liveboxandy/Gotek-Compatible-AT32F435-26Pin-SMD/STP/1188E-1K2-V-T_R.stp

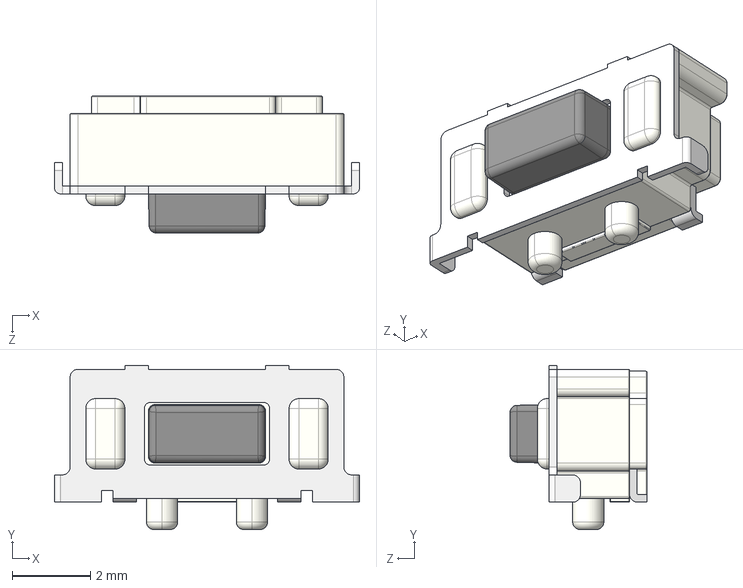
[picture p17: CAD file, 2025-10-23]
STP/1188E-1K2-V-T_R.stp
7.80 x 4.20 x 3.50 mm
