liveboxandy/Gotek-Compatible-AT32F435-26Pin-SMD/STP/SKRTLAE010.stp

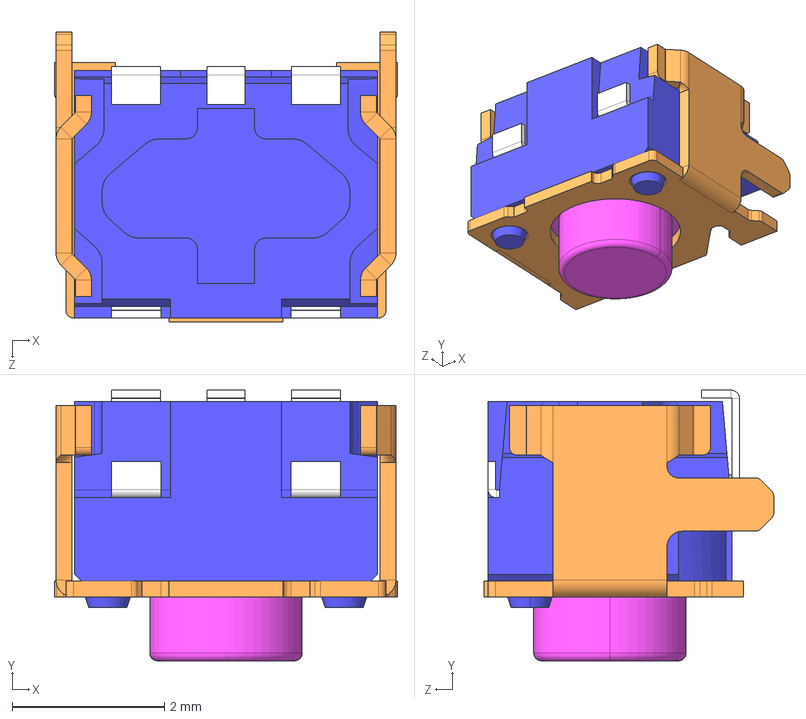
[picture p18: CAD file, 2025-10-23]
STP/SKRTLAE010.stp
4.50 x 3.55 x 3.80 mm
