liveboxandy/Gotek-Compatible-AT32F435-26Pin-SMD/STP/1N4148WS.stp

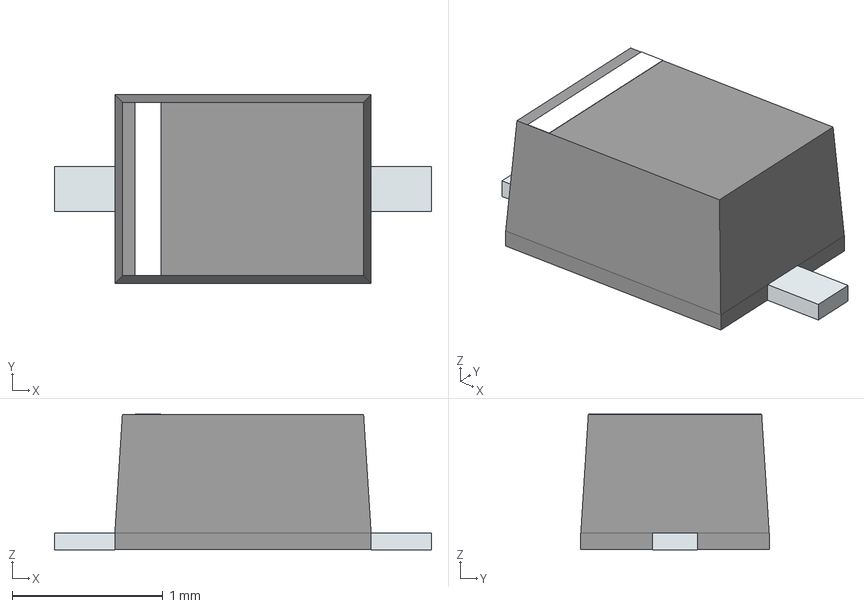
[picture p19: CAD file, 2025-10-23]
STP/1N4148WS.stp
2.50 x 1.25 x 0.9 mm
PinKIdent
PinK
PinA
