liveboxandy/Gotek-Compatible-AT32F435-26Pin-SMD/STP/Molex 2005280260.stp

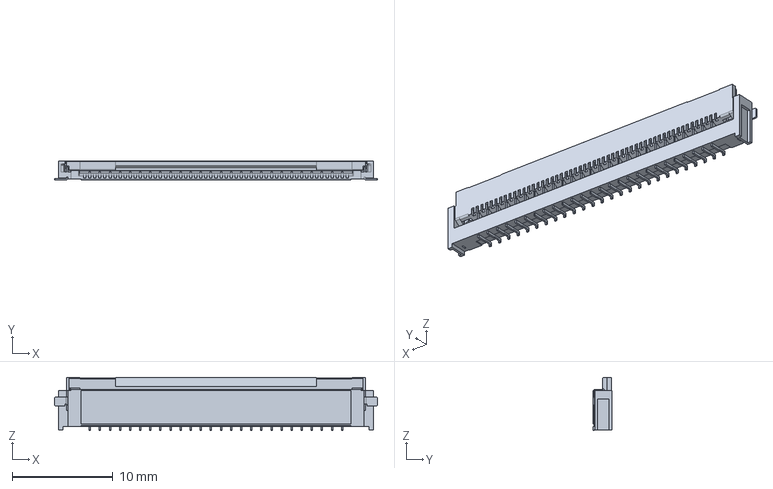
[picture p20: CAD file, 2025-10-23]
STP/Molex 2005280260.stp
32.0 x 1.90 x 5.30 mm
