liveboxandy/Gotek-Compatible-AT32F435-26Pin-SMD/STP/ABL-8.000MHZ-B2.stp

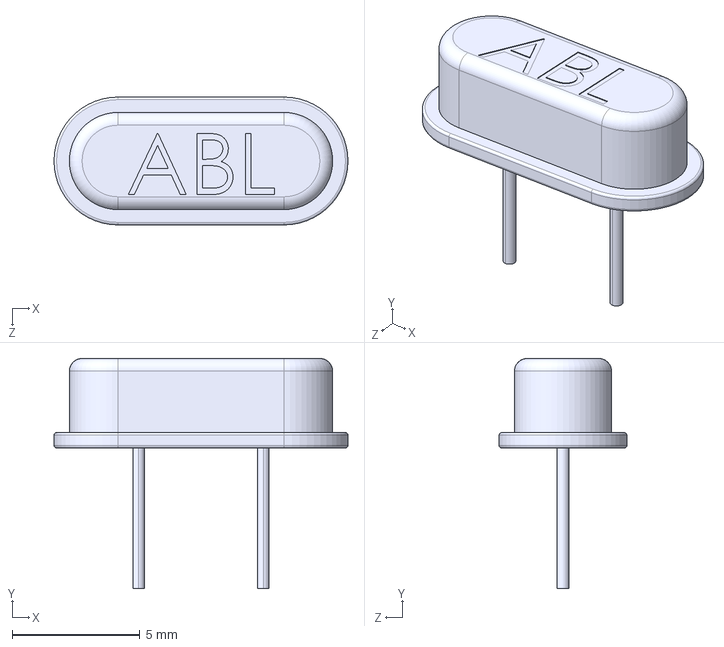
[picture p21: CAD file, 2025-10-23]
STP/ABL-8.000MHZ-B2.stp
11.5 x 9.00 x 5.00 mm
