liveboxandy/Gotek-Compatible-AT32F435-26Pin-SMD/STP/TSM-107-01-L-SH.stp

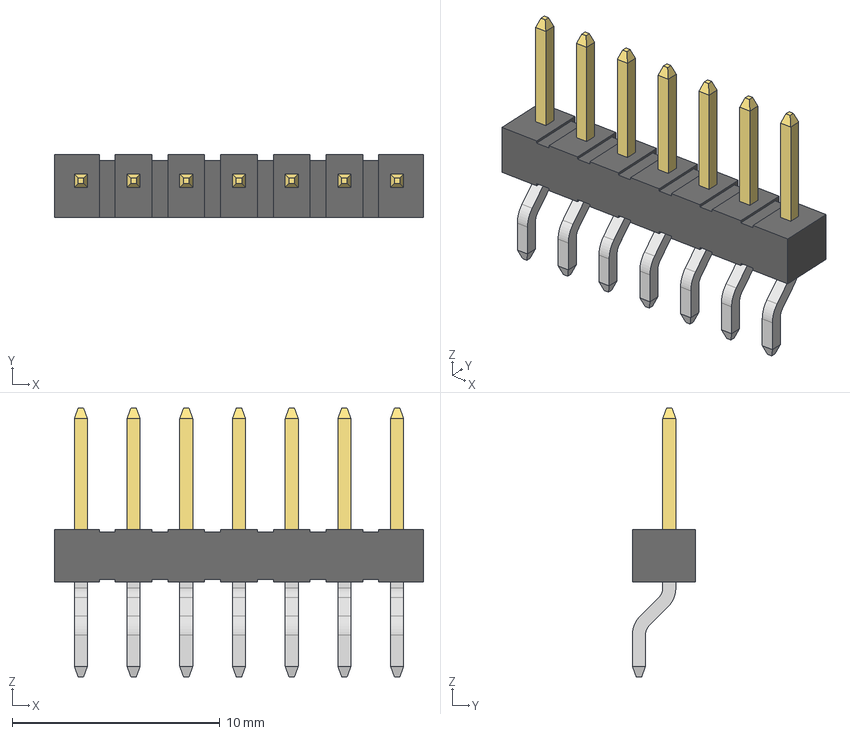
[picture p22: CAD file, 2025-10-23]
STP/TSM-107-01-L-SH.stp
17.8 x 3.05 x 13.0 mm
TSM-107-01-SH_body
T-1S6-08-L(-01-7-SH)
T-1S6-08-L(-01-7-SH)2
