liveboxandy/Gotek-Compatible-AT32F435-26Pin-SMD/STP/TSM-105-04-S-DV.stp

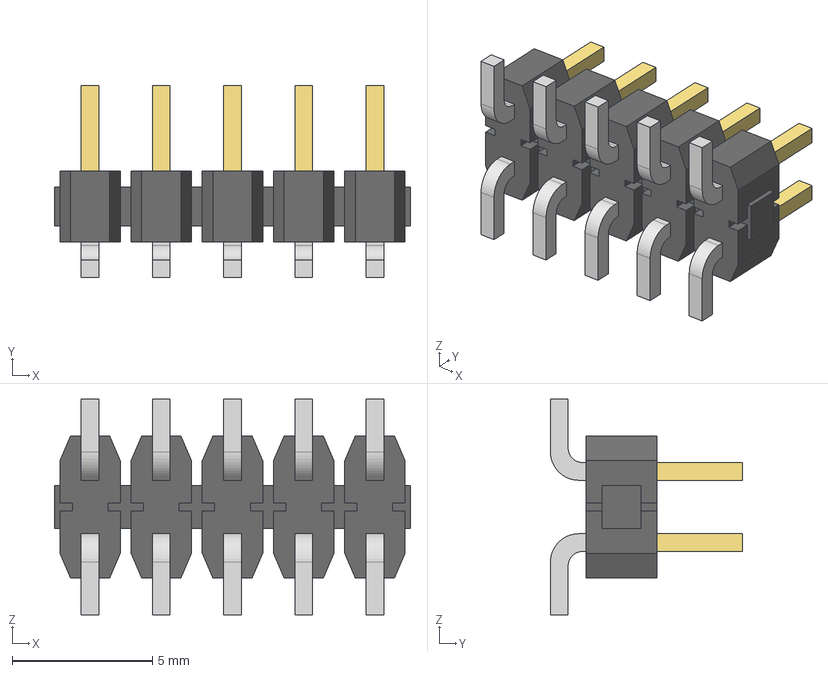
[picture p23: CAD file, 2025-10-23]
STP/TSM-105-04-S-DV.stp
12.7 x 6.86 x 7.70 mm
TSM-105-04-DV_body
T-1S6-21-S(-04-5-DV)
T-1S6-21-S(-04-5-DV)2
