liveboxandy/Gotek-Compatible-AT32F435-26Pin-SMD/STP/USB1055-GF-L-A.stp

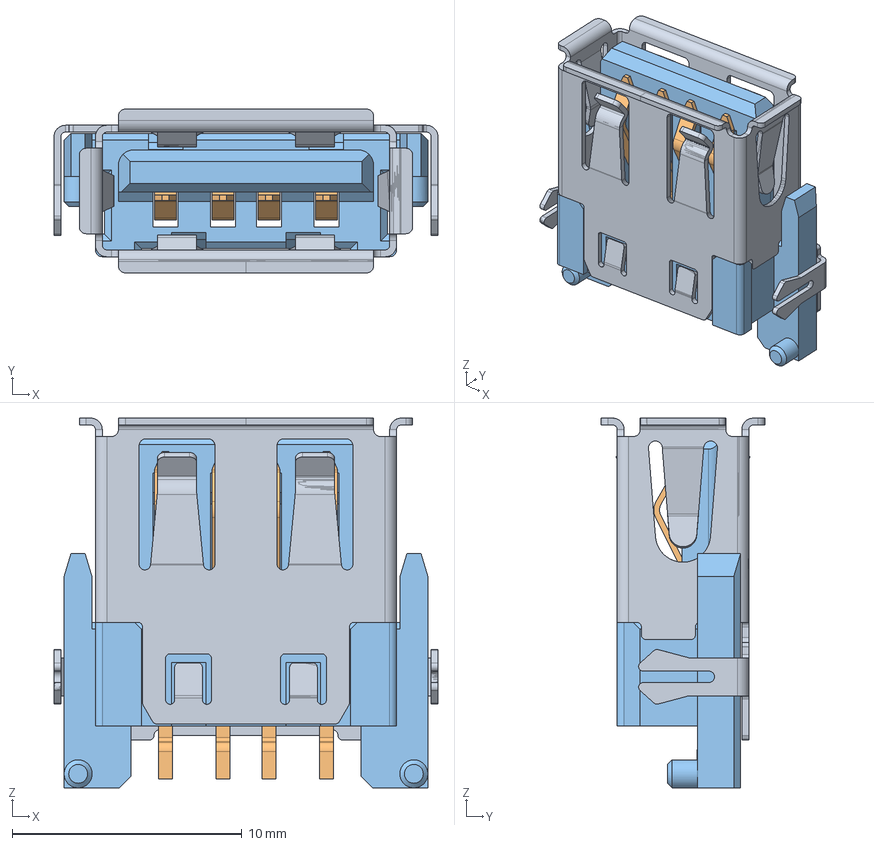
[picture p24: CAD file, 2025-10-23]
STP/USB1055-GF-L-A.stp
16.7 x 7.12 x 16.1 mm
USB1055-GF-L-A_PART8
USB1055-GF-L-A_PART7
USB1055-GF-L-A_PART6
USB1055-GF-L-A_PART5
USB1055-GF-L-A_PART4
USB1055-GF-L-A_PART3
USB1055-GF-L-A_PART2
USB1055-GF-L-A_PART1
