liveboxandy/Gotek-Compatible-AT32F435-26Pin-SMD/3V3To5VConversion.kicad_sch

## KiCad design 3V3To5VConversion.kicad_sch (2025-10-23)

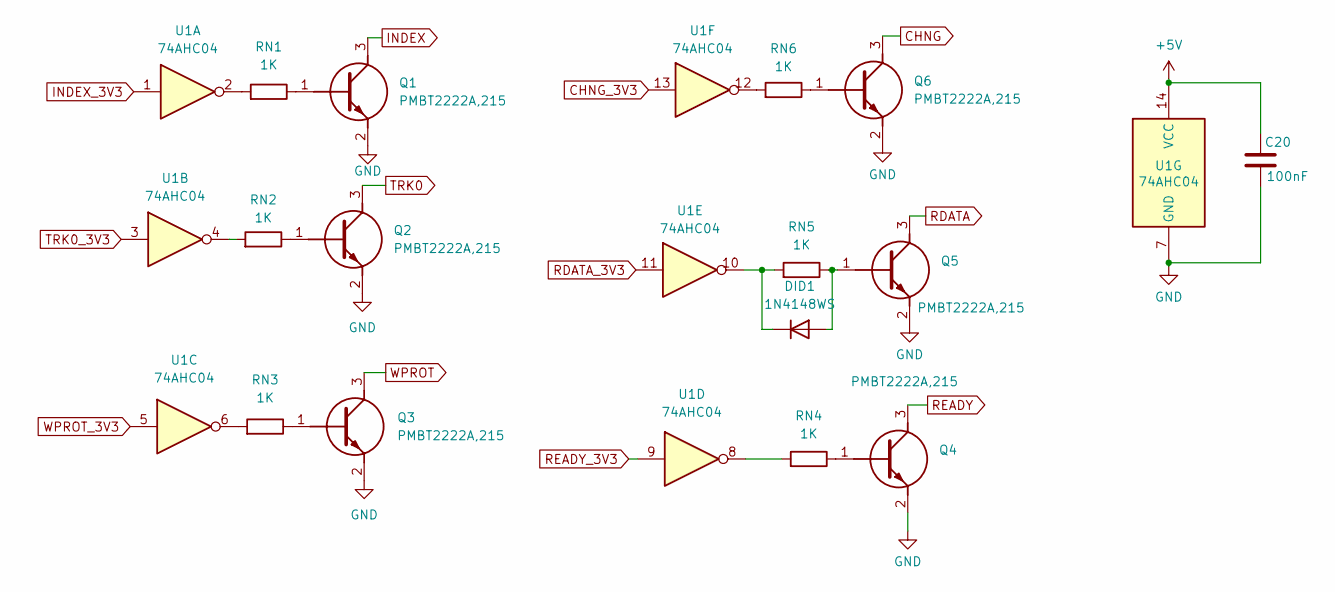
[picture p28: schematic 3V3To5VConversion.kicad_sch]

Parts:
C20: 100nF; C_0805_2012Metric_Pad1.18x1.45mm_HandSolder
DID1: 1N4148WS; SODFL2512X90N
Q1, Q2, Q3, Q4, Q5, Q6: PMBT2222A,215; SOT95P280X130-3N; Mouser Part Number 771-PMBT2222A-T/R
RN1, RN2, RN3, RN4, RN5, RN6: 1K; R_0805_2012Metric_Pad1.20x1.40mm_HandSolder
U1: 74AHC04; SO-14_3.9x8.65mm_P1.27mm

Connections:
+5V: C20.2, U1.14 (VCC)
CHNG: Q6.3 (C)
CHNG_3V3: U1.13
GND: C20.1, Q1.2 (E), Q2.2 (E), Q3.2 (E), Q4.2 (E), Q5.2 (E), Q6.2 (E), U1.7 (GND)
INDEX: Q1.3 (C)
INDEX_3V3: U1.1
unnamed: DID1.1 (K), RN5.2, U1.10
unnamed: DID1.2 (A), Q5.1 (B), RN5.1
unnamed: Q1.1 (B), RN1.1
unnamed: Q2.1 (B), RN2.1
unnamed: Q3.1 (B), RN3.1
unnamed: Q4.1 (B), RN4.1
unnamed: Q6.1 (B), RN6.1
unnamed: RN1.2, U1.2
unnamed: RN2.2, U1.4
unnamed: RN3.2, U1.6
unnamed: RN4.2, U1.8
unnamed: RN6.2, U1.12
RDATA: Q5.3 (C)
RDATA_3V3: U1.11
READY: Q4.3 (C)
READY_3V3: U1.9
TRK0: Q2.3 (C)
TRK0_3V3: U1.3
WPROT: Q3.3 (C)
WPROT_3V3: U1.5
