liveboxandy/Gotek-Compatible-AT32F435-26Pin-SMD/Gotek.kicad_sch

## KiCad design Gotek.kicad_sch (2025-10-23)

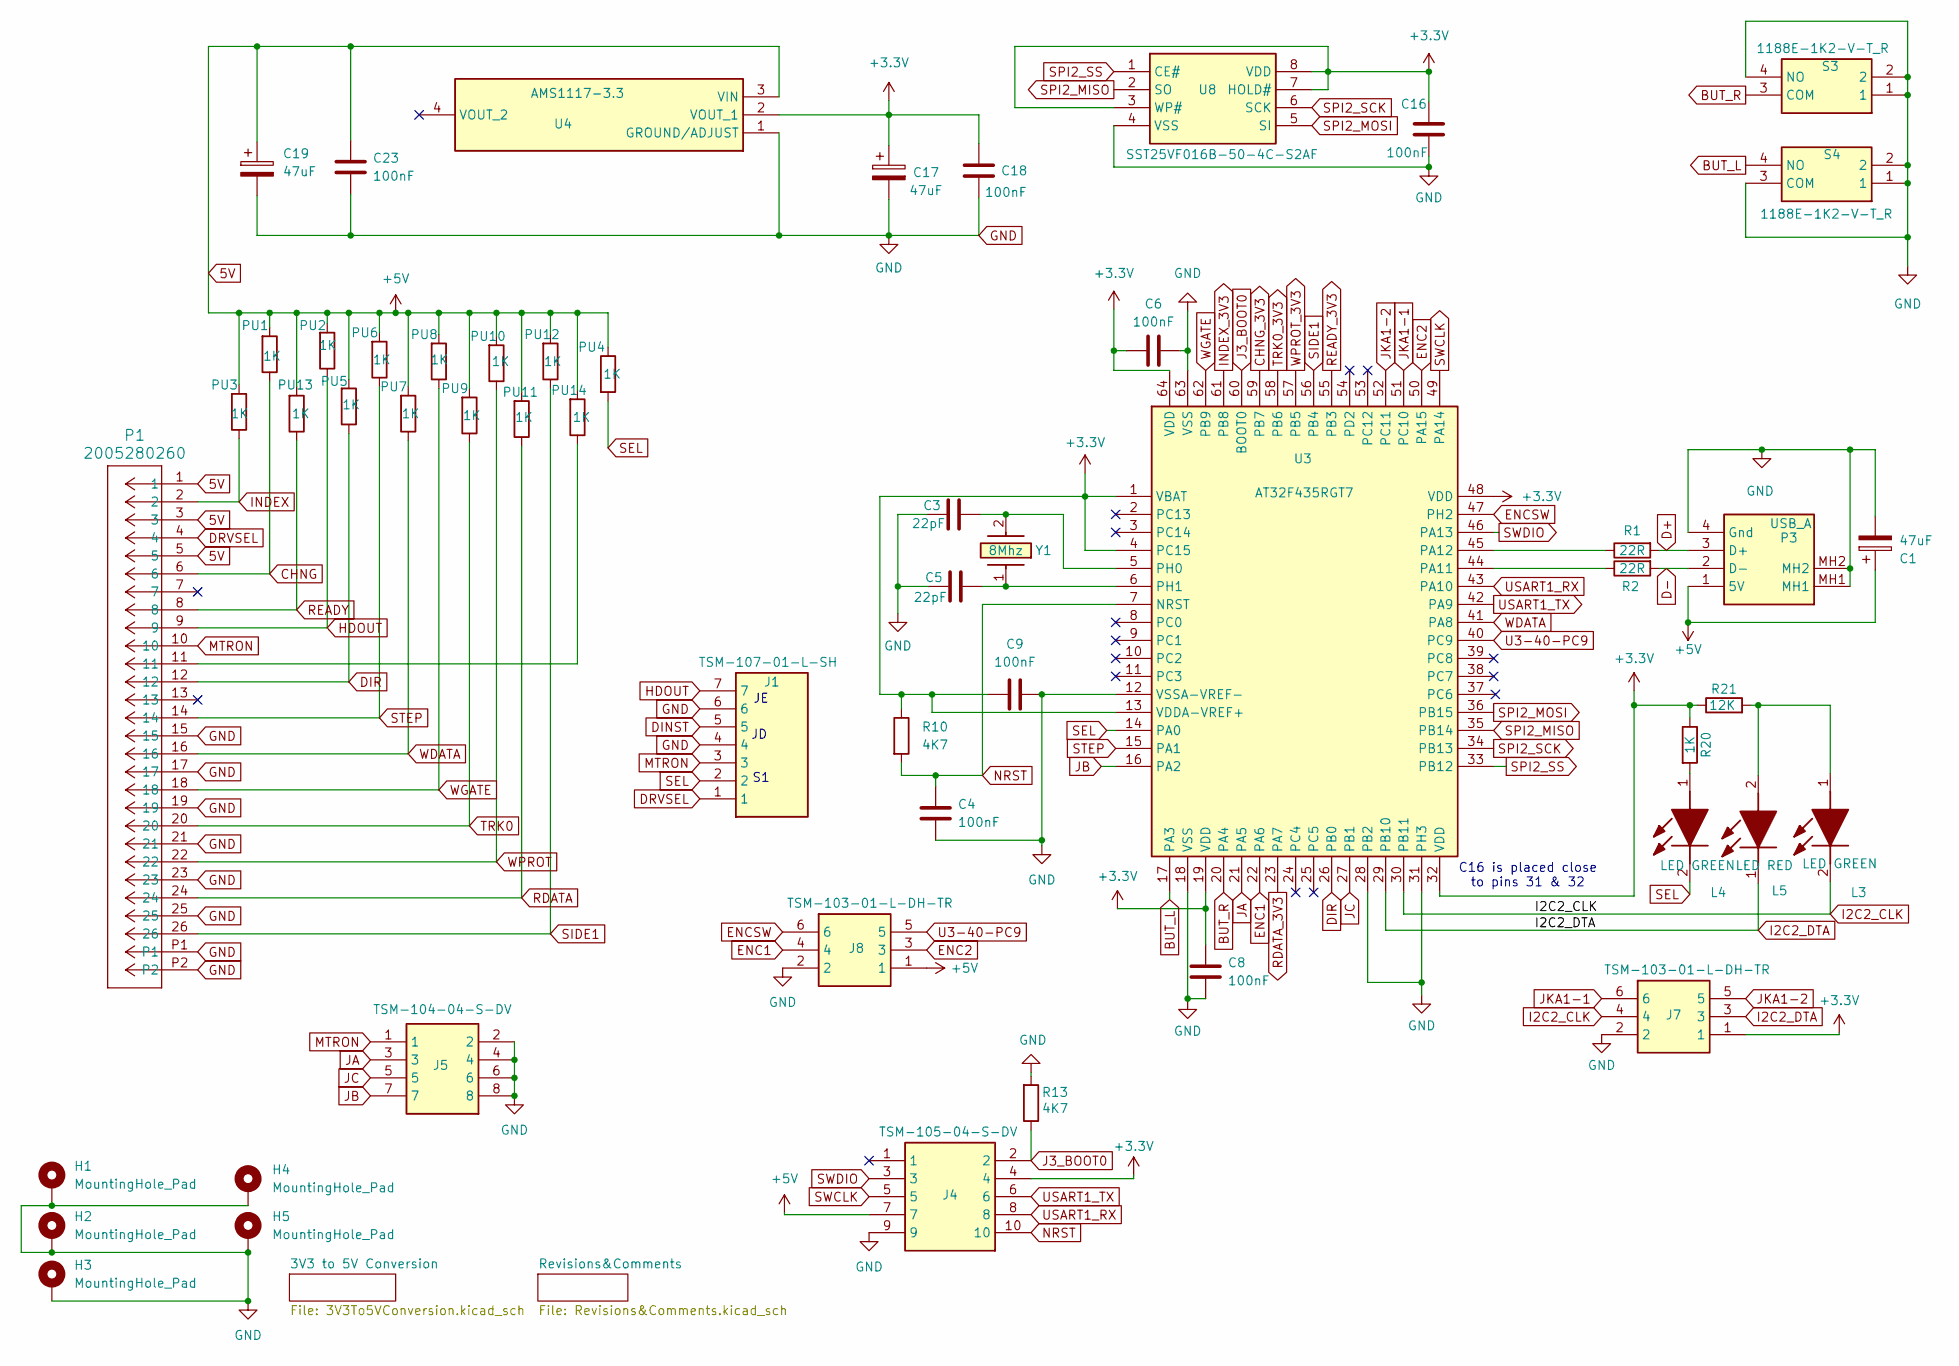
[picture p29: schematic Gotek.kicad_sch]

Parts:
C1, C17, C19: 47uF; CP_EIA-3528-21_Kemet-B_Pad1.50x2.35mm_HandSolder
C3, C5: 22pF; C_0805_2012Metric_Pad1.18x1.45mm_HandSolder
C4, C6, C8, C9, C16, C18, C23: 100nF; C_0805_2012Metric_Pad1.18x1.45mm_HandSolder
H1, H2, H3, H4, H5: MountingHole_Pad; MountingHole_M3_Pad
J1: TSM-107-01-L-SH; Mouser Part Number 200-TSM10701LSH
J4: TSM-105-04-S-DV; Mouser Part Number 200-TSM10504SDV
J5: TSM-104-04-S-DV; Mouser Part Number 200-TSW10405LD
J7, J8: TSM-103-01-L-DH-TR; Mouser Part Number 200-TSM10301LDHTR
L3, L4: LED GREEN; APT2012PGW; Mouser Part Number 604-APT2012PGW
L5: LED RED; HSMCC177; Mouser Part Number 630-HSMC-C177
P1: 2005280260; MOLEX_CON_2005280260
P3: USB_A; USB1046GF0190LBA; Mouser Part Number 640-USB1046GF0190LBA
PU1, PU2, PU3, PU4, PU5, PU6, PU7, PU8, PU9, PU10, PU11, PU12, PU13, PU14: 1K; R_0805_2012Metric_Pad1.20x1.40mm_HandSolder
R1, R2: 22R; R_0805_2012Metric_Pad1.20x1.40mm_HandSolder
R10, R13: 4K7; R_0805_2012Metric_Pad1.20x1.40mm_HandSolder
R20: 1K; R_0805_2012Metric_Pad1.20x1.40mm_HandSolder
R21: 12K; R_0805_2012Metric_Pad1.20x1.40mm_HandSolder
S3, S4: 1188E-1K2-V-T_R; 1188E1K2VTR; Mouser Part Number 113-1188E1K2VTR
U3: AT32F435RGT7; QFP50P1200X1200X160-64N; Manufacturer_Part_Number AT32F435RGT7
U4: AMS1117-3.3; SOT229P700X180-4N; Manufacturer_Part_Number ams1117-3.3v
U8: SST25VF016B-50-4C-S2AF; SOIC127P790X216-8N; Mouser Part Number 579-25VF016B504CS2AF
Y1: 8Mhz; LFXTAL050985Bulk; Mouser Part Number 449-LFXTAL050985BULK

Connections:
+3.3V: C6.1, C8.1, C9.2, C16.2, C17.1, C18.2, J4.4, J7.1, R10.1, R20.1, R21.1, U3.1 (VBAT), U3.4 (PC15), U3.13 (VDDA-VREF+), U3.19 (VDD), U3.32 (VDD), U3.48 (VDD), U3.64 (VDD), U4.2 (VOUT_1), U8.3 (WP#), U8.7 (HOLD#), U8.8 (VDD)
+5V: C1.1, C19.1, C23.1, J4.7, J8.1, P1.1, P1.3, P1.5, P3.1 (5V), PU1.2, PU2.2, PU3.2, PU4.1, PU5.2, PU6.2, PU7.2, PU8.2, PU9.2, PU10.2, PU11.2, PU12.2, PU13.2, PU14.2, U4.3 (VIN)
BUT_L: S4.4 (NO), U3.17 (PA3)
BUT_R: S3.3 (COM), U3.20 (PA4)
CHNG: P1.6, PU1.1
CHNG_3V3: U3.59 (PB7)
D+: P3.3 (D+), R1.2
D-: P3.2 (D-), R2.2
DINST: J1.5
DIR: P1.12, PU5.1, U3.26 (PB0)
DRVSEL: J1.1, P1.4
ENC1: J8.4, U3.22 (PA6)
ENC2: J8.3, U3.50 (PA15)
ENCSW: J8.6, U3.47 (PH2)
GND: C1.2, C3.1, C4.2, C5.2, C6.2, C8.2, C9.1, C16.1, C17.2, C18.1, C19.2, C23.2, H1.1, H2.1, H3.1, H4.1, H5.1, J1.4, J1.6, J4.9, J5.2, J5.4, J5.6, J5.8, J7.2, J8.2, P1.15, P1.17, P1.19, P1.21, P1.23, P1.25, P1.P1, P1.P2, P3.4 (Gnd), P3.MH1, P3.MH2, R13.2, S3.1, S3.2, S3.4 (NO), S4.1, S4.2, S4.3 (COM), U3.12 (VSSA-VREF-), U3.18 (VSS), U3.28 (PB2), U3.31 (PH3), U3.63 (VSS), U4.1 (GROUND/ADJUST), U8.4 (VSS)
HDOUT: J1.7, P1.9, PU2.1
I2C2_CLK: J7.4, L3.2 (K), U3.30 (PB11)
I2C2_DTA: J7.3, L5.1 (K), U3.29 (PB10)
INDEX: P1.2, PU3.1
INDEX_3V3: U3.61 (PB8)
J3_BOOT0: J4.2, R13.1, U3.60 (BOOT0)
JA: J5.3, U3.21 (PA5)
JB: J5.7, U3.16 (PA2)
JC: J5.5, U3.27 (PB1)
JKA1-1: J7.6, U3.51 (PC10)
JKA1-2: J7.5, U3.52 (PC11)
MTRON: J1.3, J5.1, P1.10
NRST: C4.1, J4.10, R10.2, U3.7 (NRST)
unnamed: C3.2, U3.5 (PH0), Y1.2
unnamed: C5.1, U3.6 (PH1), Y1.1
unnamed: L3.1 (A), L5.2 (A), R21.2
unnamed: L4.1 (A), R20.2
unnamed: P1.11, PU14.1
unnamed: R1.1, U3.45 (PA12)
unnamed: R2.1, U3.44 (PA11)
RDATA: P1.24, PU11.1
RDATA_3V3: U3.23 (PA7)
READY: P1.8, PU13.1
READY_3V3: U3.55 (PB3)
SEL: J1.2, L4.2 (K), PU4.2, U3.14 (PA0)
SIDE1: P1.26, PU12.1, U3.56 (PB4)
SPI2_MISO: U3.35 (PB14), U8.2 (SO)
SPI2_MOSI: U3.36 (PB15), U8.5 (SI)
SPI2_SCK: U3.34 (PB13), U8.6 (SCK)
SPI2_SS: U3.33 (PB12), U8.1 (CE#)
STEP: P1.14, PU6.1, U3.15 (PA1)
SWCLK: J4.5, U3.49 (PA14)
SWDIO: J4.3, U3.46 (PA13)
TRK0: P1.20, PU9.1
TRK0_3V3: U3.58 (PB6)
U3-40-PC9: J8.5, U3.40 (PC9)
USART1_RX: J4.8, U3.43 (PA10)
USART1_TX: J4.6, U3.42 (PA9)
WDATA: P1.16, PU7.1, U3.41 (PA8)
WGATE: P1.18, PU8.1, U3.62 (PB9)
WPROT: P1.22, PU10.1
WPROT_3V3: U3.57 (PB5)

Notes on the sheet:
C16 is placed close to pins 31 & 32
